ellak-monades-aristeias/WeatherXM/D2-WeatherStation/DSC_0124.JPG

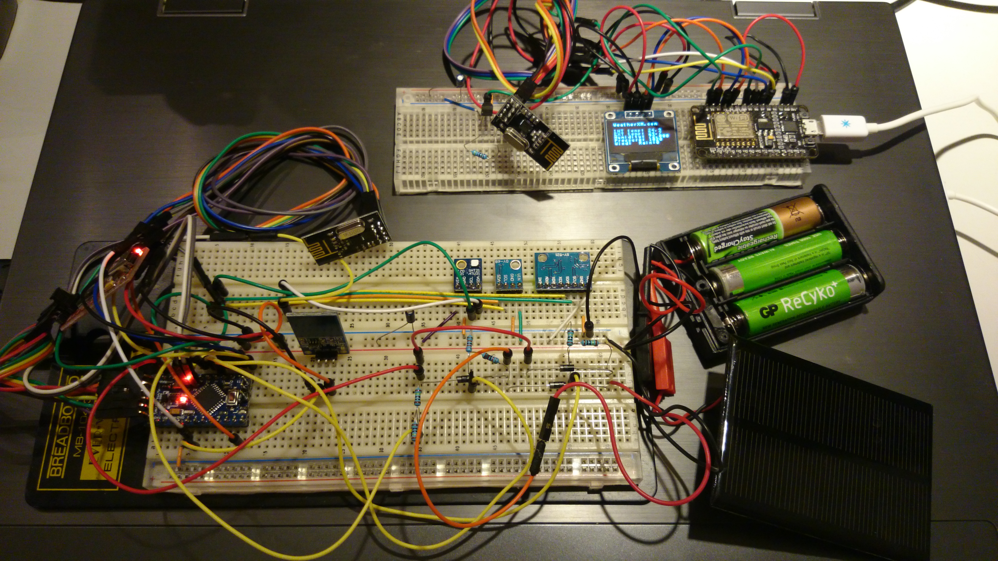
D2-WeatherStation/DSC_0124.JPG
