ellak-monades-aristeias/WeatherXM/D1-Evaluation/DSC_0149.JPG

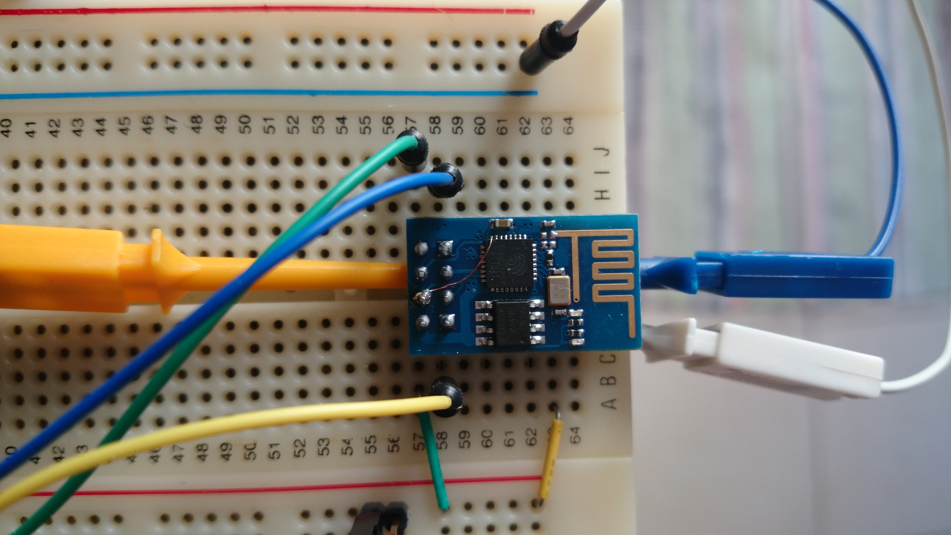
D1-Evaluation/DSC_0149.JPG
