ellak-monades-aristeias/WeatherXM/D1-Evaluation/DSC_0163.JPG

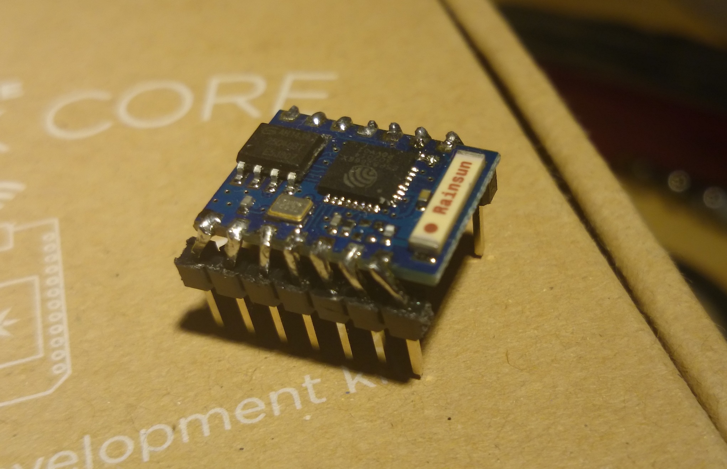
D1-Evaluation/DSC_0163.JPG
